GleisMon/wordclock-de/firmware/Wortuhr/certs.h

#pragma once
// Root CAs for the GitHub update download; regenerate with tools/make_certs.py if GitHub changes its CAs.
// Taken from the Mozilla CA bundle.
static const char GH_CA_GITHUB[] PROGMEM = R"PEM(
-----BEGIN CERTIFICATE-----
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
-----END CERTIFICATE-----
-----BEGIN CERTIFICATE-----
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
-----END CERTIFICATE-----
)PEM";
static const char GH_CA_ASSETS[] PROGMEM = R"PEM(
-----BEGIN CERTIFICATE-----
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
-----END CERTIFICATE-----
)PEM";
