GleisMon/wordclock-de/firmware/Wortuhr/version.h

#pragma once
// Bump together with the git tag (vX.Y.Z); CI refuses a tag that does not match.
#define FW_VERSION "0.1.5"
#define FW_REPO "GleisMon/wordclock-de"
#define FW_ASSET "wortuhr-de.bin"
#define FW_NAME "Wortuhr"
